plopezmarin/TFG-Robot-educativo/BLE/ble_servidor_mando.h

/*
LIBRERIA PARA EL BLUETOOTH - PARTE DEL MANDO (CLIENTE)
*/

#ifndef bleMando_h
#define bleMando_h
 
#include "Arduino.h"
#include "BLEDevice.h"
#include <BLEUtils.h>
#include <BLEServer.h>

//joystick
extern const int SW_pin; // digital pin connected to switch output
extern const int X_pin; // analog pin connected to X output
extern const int Y_pin; // analog pin connected to Y output

/*FUNCIÓN DEL DRIVER
Esta función obtiene la posición del joystick, divide cada eje en 5 partes
devuelve la posición a modo de coordenadas. En reposo = 33*/
String control_mando();

/*FUNCION COMUNICACION
Esta función notifica la caracteristica*/
void envia_movimiento_ble(String mov_notify);

/*FUNCION DE INICIALIZACION DEL BLE SERVIDOR
Esta función inicializa el protocolo BLE de la parte del servidor (mando)*/
void inicializa_ble_mando();

#endif
