plopezmarin/TFG-Robot-educativo/BLE/Ejemplo_coche/Ejemplo_coche.ino

#include <ble_cliente_coche.h>

void setup() {
  // put your setup code here, to run once:
  Serial.begin(115200);

  inicializa_motores();     //Es necesario llamar al driver para inicilizar los motores
  inicializa_ble_coche();

}

void loop() {
  // put your main code here, to run repeatedly:
  control_coche();

}
