plopezmarin/TFG-Robot-educativo/Comunicacion_serial_camara/Ejemplo/Ejemplo.ino

#include <comunicacion_camara.h>


void setup() {
  // put your setup code here, to run once:
  inicializa_camara();
  //randomSeed(0);
}

void loop() {
  // put your main code here, to run repeatedly:
  bool goal = false;  //este flag indica si hemos encontrado todos los tags
  bool flag_encontrado = false;
  char random_accion[2] = { 'R', 'L' };  //conjunto de posibles acciones aleatorias
  int objetivo[3] = { 0, 2, 3 };         //Tags que queremos encontrar por el orden dado
  int obj_actual = 0;
  float distancia_tag;  //varible que almacena la distancia
  float posicion_x;     //varible que almacenea la posición en X
  int elementos;        //variable que almacena el número de tags detectados


  while (!goal) {
    //Obtener un array de los tags detectados
    struct tag_struct *array_TAG = detecta_tag(&elementos);
    //ordena_tags(arrayTAGs, n_tags, ID, ASCENDENTE);

    //ver si el tag que estamos buscando esta en las detecciones
    flag_encontrado = busca_id(array_TAG, objetivo[obj_actual], &distancia_tag, &posicion_x);
    //IMPORTANTE: liberar la memoria del tag de las detecciones
    free(array_TAG);

    if (!flag_encontrado) {  //no se ha encontrado
      int r_a = random(2);
      int r_v = random(50, 56);
      int r_t = (0.3 + rand() % 2);

      comunicacion(random_accion[r_a], r_v, r_t);  //girar al azar

      comunicacion('F', 55, 0.5);
    } else {  //Si encontrado
      //Alinear al robot con el tag
      if (posicion_x < -0.2) {
        comunicacion('L', 52, 0.1);
      } else if (posicion_x > 0.2) {
        comunicacion('R', 52, 0.1);
      }
      //sonar buzzer
      buzzer(2489, 2);
      //avanzar hacia el tag
      comunicacion('F', 55, 2.5 * distancia_tag);

      comunicacion('B', 55, 2);
      obj_actual++;
      comunicacion('R', 60, 4);  //girar sobre sí mismo
      if (obj_actual > 3) goal = true;
    }
  }
  //free(array_TAG);
}
